StrikeEagleCC/lynx_blaster_custom_parts/parts/Tighter Rail 1 (customized).SLDPRT

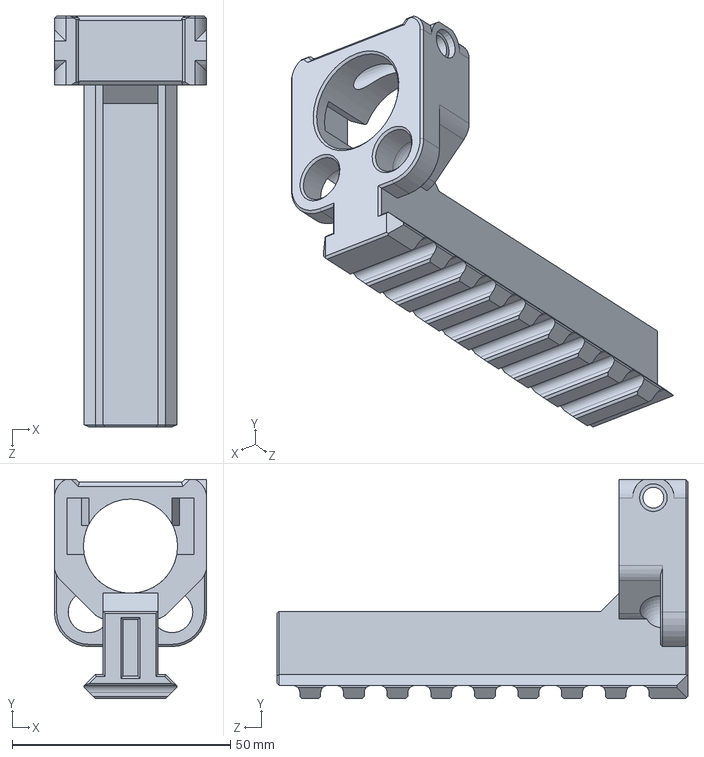
[picture p14: CAD file, 2023-05-31]
parts/Tighter Rail 1 (customized).SLDPRT
34.9 x 50.3 x 94.2 mm
