StrikeEagleCC/lynx_blaster_custom_parts/parts/Catch 3 (customized).SLDPRT

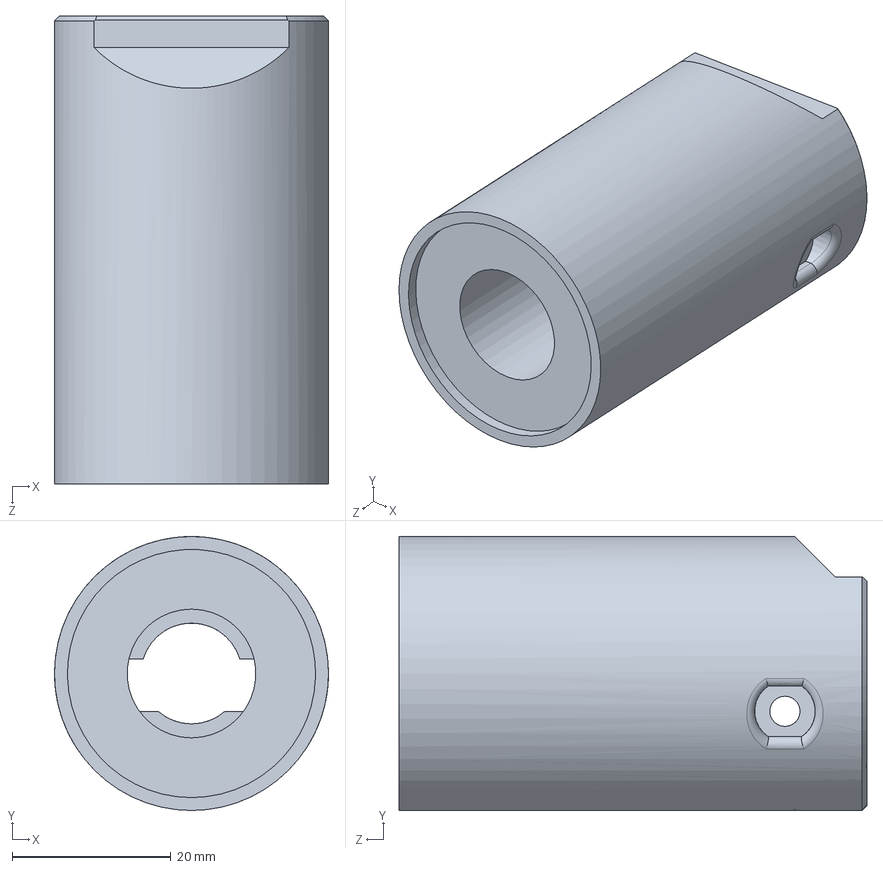
[picture p15: CAD file, 2023-05-31]
parts/Catch 3 (customized).SLDPRT
34.5 x 34.5 x 58.9 mm
