StrikeEagleCC/lynx_blaster_custom_parts/parts/Sear (customized).SLDPRT

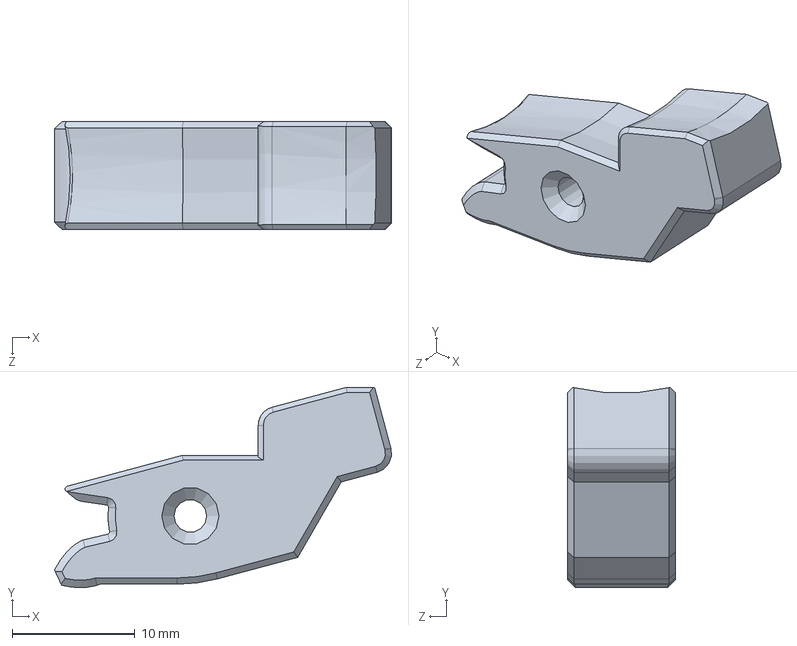
[picture p16: CAD file, 2023-05-31]
parts/Sear (customized).SLDPRT
27.4 x 16.3 x 8.76 mm
